svenpetersen1965/C64-Expansion-Port-Extension/C64 Expansion Port Extension/Cartridge Side/Rev. 0/pictures/4250_-_Versa64Cart_25.JPG

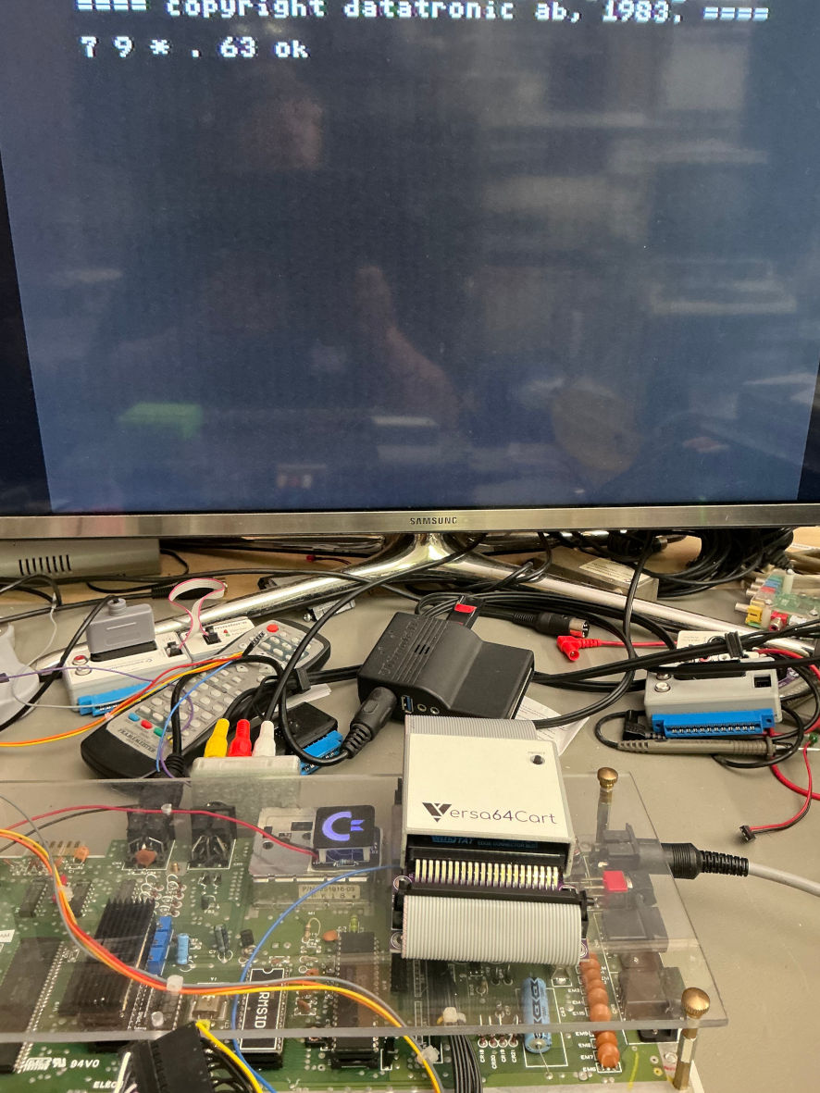
C64 Expansion Port Extension/Cartridge Side/Rev. 0/pictures/4250_-_Versa64Cart_25.JPG
