svenpetersen1965/C64-Expansion-Port-Extension/C64 Expansion Port Extension/Cartridge Side/Rev. 0/pictures/4253_-_KungFuFlash100.JPG

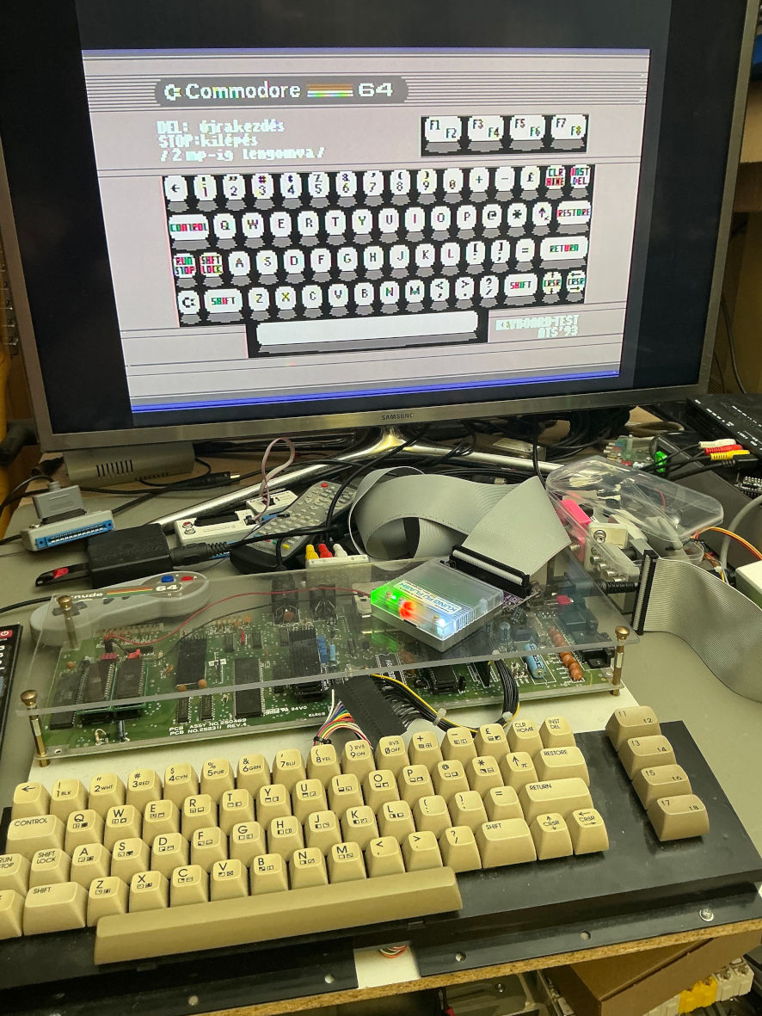
C64 Expansion Port Extension/Cartridge Side/Rev. 0/pictures/4253_-_KungFuFlash100.JPG
