svenpetersen1965/C64-Expansion-Port-Extension/C64 Expansion Port Extension/Cartridge Side/Rev. 0/pictures/4257_-_UltimateII_100.JPG

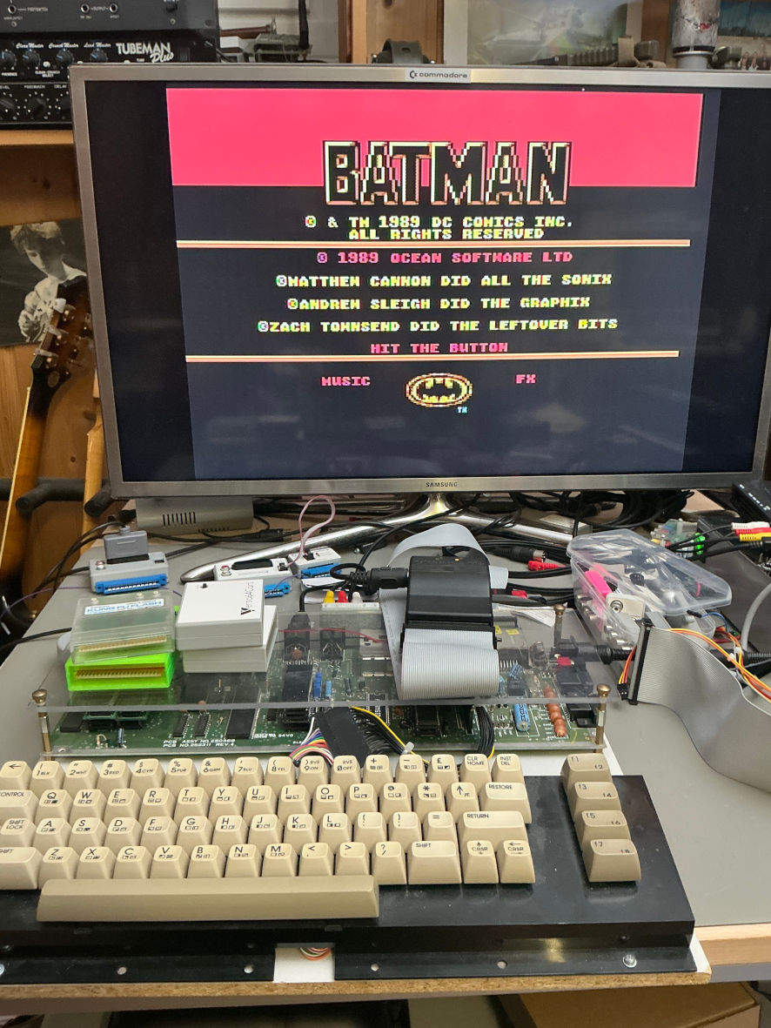
C64 Expansion Port Extension/Cartridge Side/Rev. 0/pictures/4257_-_UltimateII_100.JPG
