svenpetersen1965/C64-Expansion-Port-Extension/C64 Expansion Port Extension/Cartridge Side/Rev. 0/pictures/4262_-_Kernal64cart25.JPG

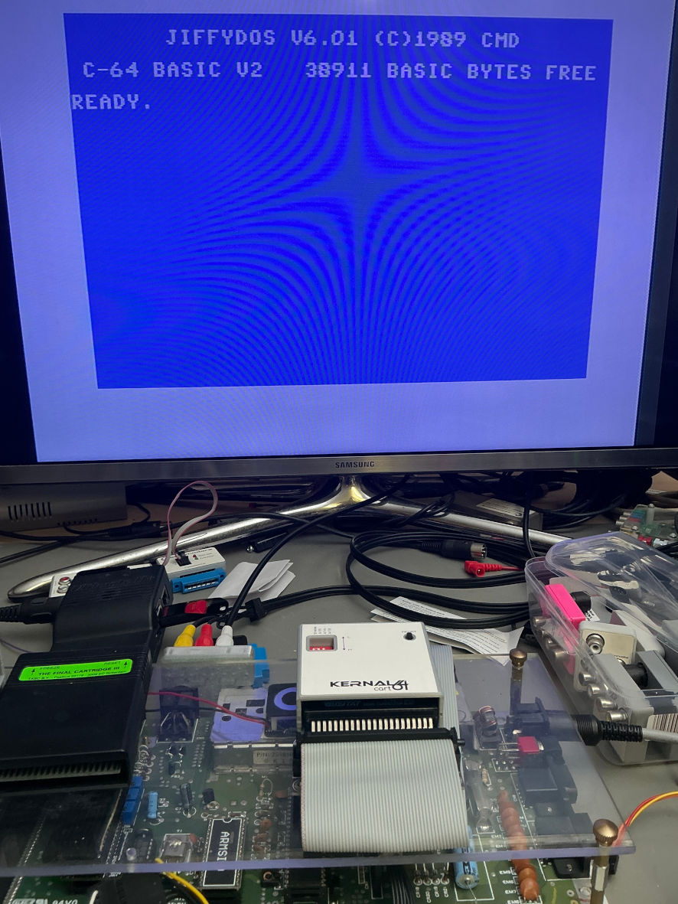
C64 Expansion Port Extension/Cartridge Side/Rev. 0/pictures/4262_-_Kernal64cart25.JPG
