svenpetersen1965/C64-Expansion-Port-Extension/C64 Expansion Port Extension/Cartridge Side/Rev. 0/pictures/4268_-_PowerCartridge25.JPG

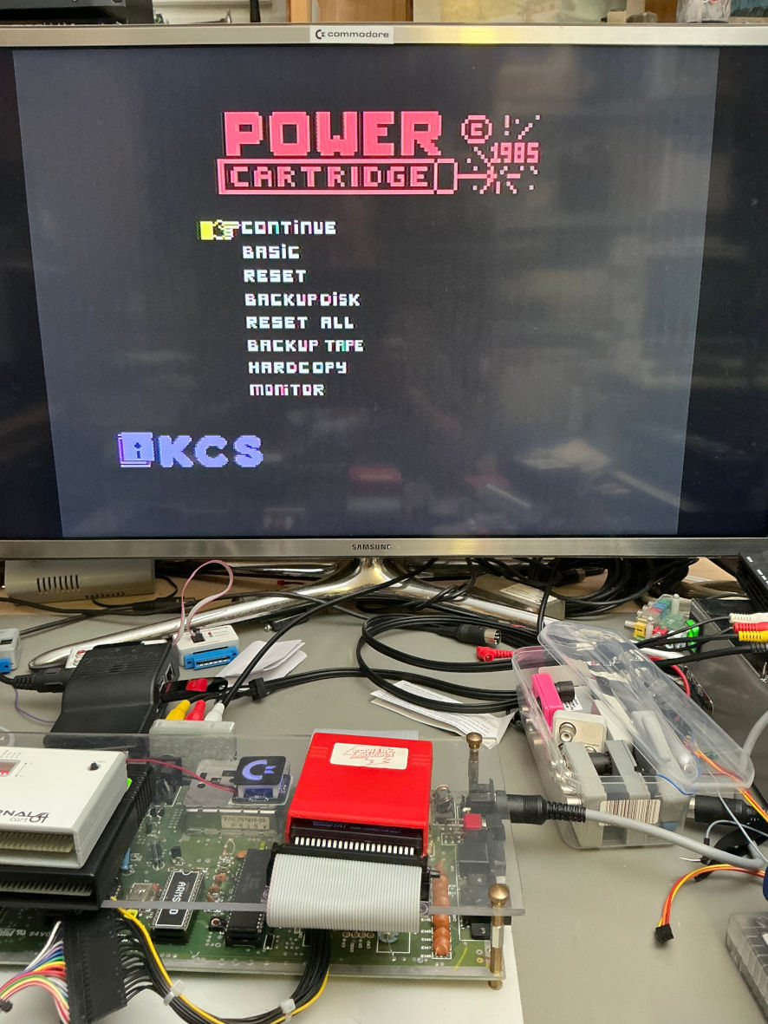
C64 Expansion Port Extension/Cartridge Side/Rev. 0/pictures/4268_-_PowerCartridge25.JPG
